sandman72/micropython_demoboard/Software/Demos/02_PWM_LED_Demo.py

# Bibliotheken laden
from machine import Pin, PWM
from time import sleep_ms

# Blaue LED an GPIO22 mit PWM initialisieren
pwm = PWM(Pin(22))

# Frequenz (Hz) einstellen
pwm.freq(4000)

# Endlosschleife LED Helligkeit hoch/runterfahren
while True:
  # Helligkeit hoch fahren
  for duty_cycle in range(0, 65536, 129):
    pwm.duty_u16(duty_cycle)
    sleep_ms(3)
    
  # Helligkeit runter fahren
  for duty_cycle in range(65536, 0, -129):
    pwm.duty_u16(duty_cycle)
    sleep_ms(3)
